rowr111/triangel/firmware/shared/ir_remote_mapping.jpg

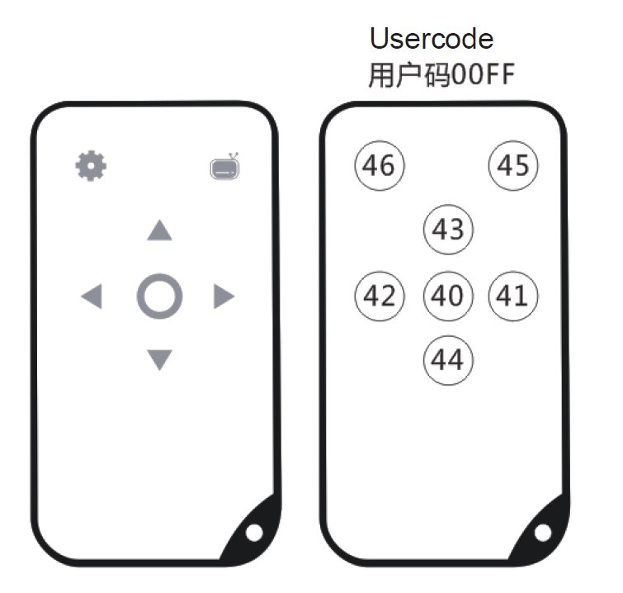
firmware/shared/ir_remote_mapping.jpg
