rowr111/triangel/graphics/triangel graphic.png

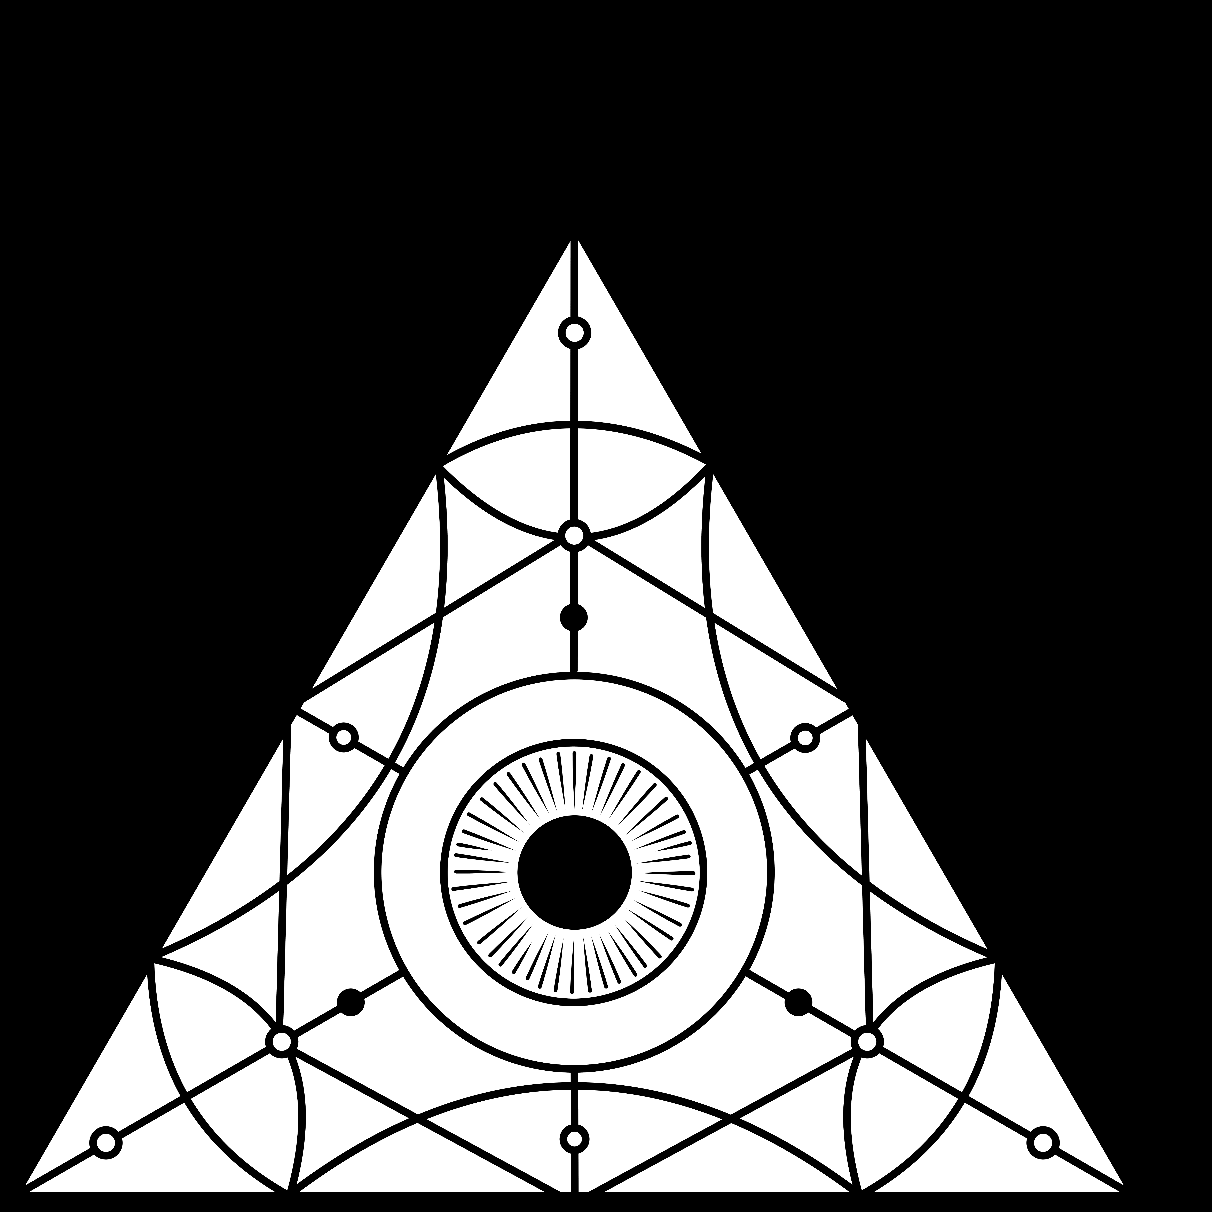
graphics/triangel graphic.png
