rowr111/triangel/graphics/triangel_input_overlay_L.jpg

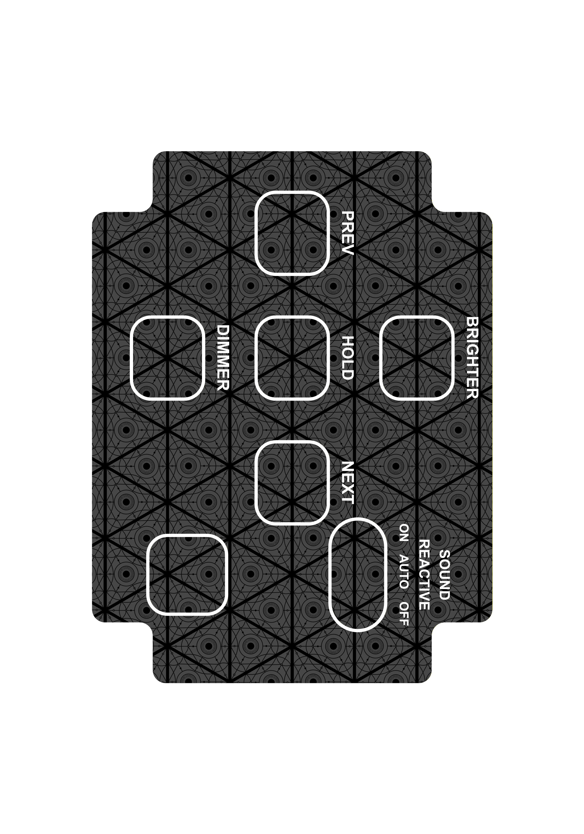
graphics/triangel_input_overlay_L.jpg
