rowr111/triangel/graphics/triangel_remote_overlay_L.jpg

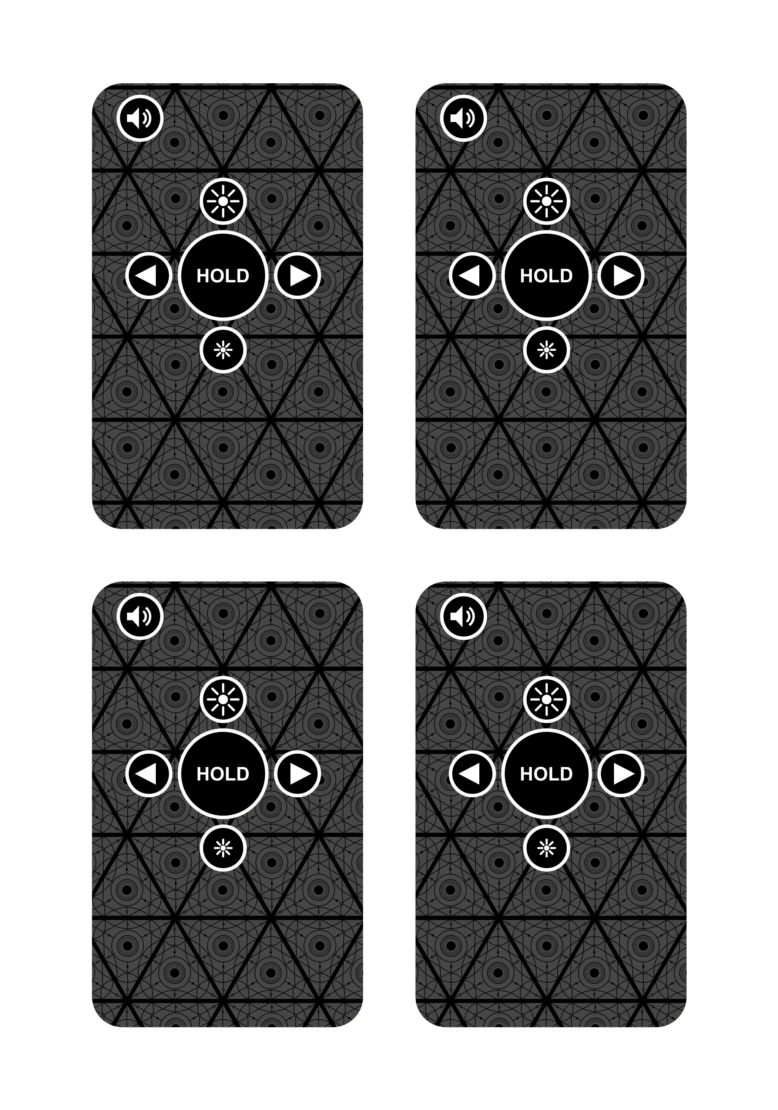
graphics/triangel_remote_overlay_L.jpg
