rowr111/triangel/graphics/triangle signature.png

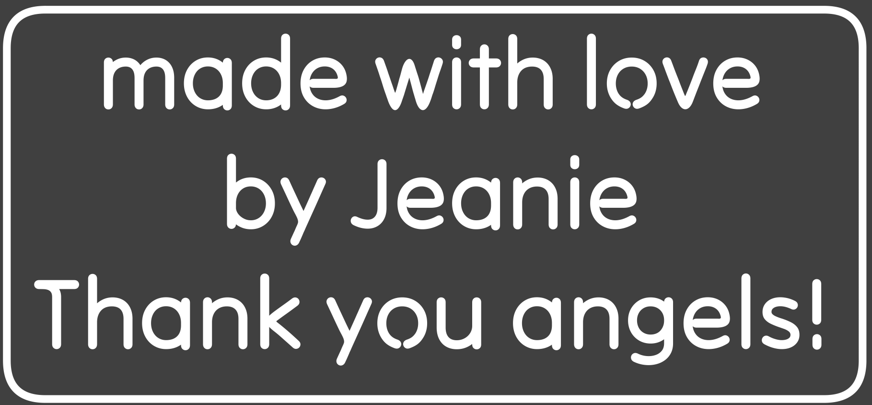
graphics/triangle signature.png
