rowr111/triangel/firmware/eye/src/patterns/ambient/flame.rs

use crate::led::geom::{BOARD_COUNT, BOARD_Y_RANGE, DIST_APEX};
use crate::patterns::{Frame, Pattern, cycle, knuth_hash, phase_phasors, ramp, PHASE_STEPS};
use crate::audio::Audio;
use crate::led::map::{LED_MAP, WORLD_BOT, WORLD_CX, WORLD_H, LED_COUNT};
use core::f32::consts::{PI, TAU};

const SECOND_WAVE_STRENGTH:    f32 = 0.5;  // second wave's amplitude, relative to the first
const SECOND_WAVELENGTH_RATIO: f32 = 1.7;  // second wave's wavelength, relative to the first
const SECOND_SPEED_RATIO:      f32 = 0.63; // second wave's speed, relative to the first
const WAVE_FLOOR:   f32 = 0.35; // brightness left in the wave troughs
const HEAT_BIAS:    f32 = 0.45; // heat added everywhere
const COOL_TILT:    f32 = 0.35;  // heat taken off at the top of the fixture
const TILE_TILT:    f32 = 0.25; // heat taken off at the top of each tile
const FLICKER_DEPTH: f32 = 0.35; // flicker swing around 1.0
const FLICKER_PERIOD_MS:  u32 = 628; // two unrelated periods, so the flicker
const FLICKER2_PERIOD_MS: u32 = 401; // looks like noise
const BREATHE_DEPTH: f32 = 0.15; // slow whole-flame swell
const BREATHE_PERIOD_MS: u32 = 3_700;
// Smoke: dark wisps that rise through the flame and wander sideways.
const SMOKE_DARKEN:  f32 = 0.7;   // how dark a wisp's core gets
const SMOKE_BAND_MM: f32 = 250.0; // vertical spacing between wisps
const SMOKE_MEANDER: f32 = 2.0;   // sideways wiggle depth, in radians
const SMOKE_MEANDER_MM: f32 = 300.0; // horizontal wavelength of the wiggle
const SMOKE_EDGE0: f32 = 0.72; // field value where a wisp starts
const SMOKE_EDGE1: f32 = 0.88; // field value where it is fully dark
const SMOKE_RISE_PERIOD_MS:    u32 = 5_100; // time to climb one band spacing
const SMOKE_MEANDER_PERIOD_MS: u32 = 8_900;
// Embers and tile flares
const EMBER_COUNT: usize = 5;        // embers in flight at once
const EMBER_PERIOD_MS:  u32 = 2_600; // base flight time
const EMBER_STAGGER_MS: u32 = 977;   // added per slot, so they respawn out of step
const EMBER_RISE_MM:   f32 = 260.0;  // how far an ember climbs
const EMBER_WOBBLE_MM: f32 = 25.0;   // sideways drift while rising
const EMBER_RADIUS_MM: f32 = 28.0;
const EMBER_HEAT:      f32 = 0.55;   // heat added at the ember's center
const FLARE_PERIOD_MS: u32 = 8_300;  // one random tile flares per period
const FLARE_LEN:  f32 = 0.25;        // flare length, as a fraction of the period
const FLARE_HEAT: f32 = 0.3;         // heat added across the flaring tile

// Q12 values are x4096, so 4096 is 1.0.
const ONE: i32 = 4096;
/// The two waves' weights in their mix, Q12.
const MIX1_Q: i32 = (4096.0 / (1.0 + SECOND_WAVE_STRENGTH)) as i32;
const MIX2_Q: i32 = (4096.0 * SECOND_WAVE_STRENGTH / (1.0 + SECOND_WAVE_STRENGTH)) as i32;
const WAVE_FLOOR_Q: i32 = (WAVE_FLOOR * 4096.0) as i32;
const HEAT_BIAS_Q: i32 = (HEAT_BIAS * 4096.0) as i32;
const FLICKER_HALF_Q: i32 = (FLICKER_DEPTH * 0.5 * 4096.0) as i32;
const SMOKE_DARKEN_Q: i32 = (SMOKE_DARKEN * 4096.0) as i32;
const SMOKE_EDGE0_Q: i32 = (SMOKE_EDGE0 * 4096.0) as i32;
/// Maps SMOKE_EDGE0..SMOKE_EDGE1 onto 0..1, Q12.
const SMOKE_EDGE_SCALE_Q: i32 = (4096.0 / (SMOKE_EDGE1 - SMOKE_EDGE0)) as i32;
/// SMOKE_MEANDER in turns x65536.
const SMOKE_MEANDER_TURNS: i32 = (SMOKE_MEANDER / TAU * 65536.0) as i32;
const FLARE_HEAT_Q: f32 = FLARE_HEAT * 4096.0;
const EMBER_HEAT_Q: f32 = EMBER_HEAT * 4096.0;
/// Ember radius in 1/16 mm, its square, and 1/radius^2 scaled to give Q12.
const EMBER_R_Q4: i32 = (EMBER_RADIUS_MM * 16.0) as i32;
const EMBER_R2_Q8: i32 = EMBER_R_Q4 * EMBER_R_Q4;
const EMBER_INV_R2: i32 = (4096 << 16) / EMBER_R2_Q8;

/// Sine table entries per turn; a phase in turns x65536 indexes it by its top bits.
const SIN_BITS: u32 = 10;
const SIN_STEPS: usize = 1 << SIN_BITS;
/// Fire ramp table entries across heat 0..1, plus one for exactly 1.0.
const RAMP_BITS: u32 = 10;
const RAMP_STEPS: usize = (1 << RAMP_BITS) + 1;

pub struct ApexFlame {
    pub speed:      f32, // mm/s outward, first wave
    pub wavelength: f32, // mm per cycle, first wave
    // sin and cos of each LED's phase in the two waves, Q12.
    w1_sin: [i16; LED_COUNT],
    w1_cos: [i16; LED_COUNT],
    w2_sin: [i16; LED_COUNT],
    w2_cos: [i16; LED_COUNT],
    // The same for its two flicker phases, Q12.
    f1_sin: [i16; LED_COUNT],
    f1_cos: [i16; LED_COUNT],
    f2_sin: [i16; LED_COUNT],
    f2_cos: [i16; LED_COUNT],
    // The smoke wiggle's phase by x, Q12, and the smoke field's phase by y, in turns x65536.
    m_sin:   [i16; LED_COUNT],
    m_cos:   [i16; LED_COUNT],
    smoke_y: [u16; LED_COUNT],
    // Heat taken off for the LED's height in the fixture and in its tile, Q12.
    cooling: [i16; LED_COUNT],
    // Position in 1/16 mm.
    x_q4: [i16; LED_COUNT],
    y_q4: [i16; LED_COUNT],
    sin_lut:  [i16; SIN_STEPS],
    ramp_lut: [[u8; 3]; RAMP_STEPS],
}

impl ApexFlame {
    pub fn new(speed: f32, wavelength: f32) -> Self {
        let k1 = TAU / wavelength;
        let k2 = TAU / (wavelength * SECOND_WAVELENGTH_RATIO);
        let q = |v: f32| (v * 4096.0).round() as i16;
        let (fl_sin, fl_cos) = phase_phasors();
        // Two hashed flicker phases per LED; phases stepping along the chain would look
        // like a sweep.
        let hash = |i: usize| knuth_hash(LED_MAP[i].chain_idx as u32);
        let k1_of = |i: usize| (hash(i) % PHASE_STEPS as u32) as usize;
        let k2_of = |i: usize| ((hash(i) >> 16) % PHASE_STEPS as u32) as usize;
        ApexFlame {
            speed,
            wavelength,
            w1_sin: core::array::from_fn(|i| q((DIST_APEX[i] * k1).sin())),
            w1_cos: core::array::from_fn(|i| q((DIST_APEX[i] * k1).cos())),
            w2_sin: core::array::from_fn(|i| q((DIST_APEX[i] * k2).sin())),
            w2_cos: core::array::from_fn(|i| q((DIST_APEX[i] * k2).cos())),
            f1_sin: core::array::from_fn(|i| q(fl_sin[k1_of(i)])),
            f1_cos: core::array::from_fn(|i| q(fl_cos[k1_of(i)])),
            f2_sin: core::array::from_fn(|i| q(fl_sin[k2_of(i)])),
            f2_cos: core::array::from_fn(|i| q(fl_cos[k2_of(i)])),
            m_sin: core::array::from_fn(|i| q((LED_MAP[i].wx / SMOKE_MEANDER_MM * TAU).sin())),
            m_cos: core::array::from_fn(|i| q((LED_MAP[i].wx / SMOKE_MEANDER_MM * TAU).cos())),
            smoke_y: core::array::from_fn(|i| {
                (LED_MAP[i].wy / SMOKE_BAND_MM * 65536.0) as u32 as u16
            }),
            cooling: core::array::from_fn(|i| {
                let led = &LED_MAP[i];
                let height = (WORLD_BOT - led.wy) / WORLD_H; // 0 at the apex, 1 at the top row
                let (y_min, y_max) = BOARD_Y_RANGE[led.board_id as usize];
                let local_height = (y_max - led.wy) / (y_max - y_min).max(1.0);
                q(height * COOL_TILT + local_height * TILE_TILT)
            }),
            x_q4: core::array::from_fn(|i| (LED_MAP[i].wx * 16.0).round() as i16),
            y_q4: core::array::from_fn(|i| (LED_MAP[i].wy * 16.0).round() as i16),
            sin_lut: core::array::from_fn(|k| q((k as f32 / SIN_STEPS as f32 * TAU).sin())),
            ramp_lut: core::array::from_fn(|k| fire_ramp(k as f32 / (1 << RAMP_BITS) as f32)),
        }
    }
}

/// A float in -1..1 as Q12.
fn q12(v: f32) -> i32 {
    (v * 4096.0).round() as i32
}

/// sin(a + b) in Q12, from the sin and cos of each.
fn sin_sum_q12(a_sin: i16, a_cos: i16, b_sin: i32, b_cos: i32) -> i32 {
    (a_sin as i32 * b_cos + a_cos as i32 * b_sin) >> 12
}

impl Pattern for ApexFlame {
    fn render(&mut self, t_ms: u32, _audio: &Audio, out: &mut Frame) {
        // Each time term wraps at its own period first, so the f32 stays precise.
        let wl2  = self.wavelength * SECOND_WAVELENGTH_RATIO;
        let spd2 = self.speed * SECOND_SPEED_RATIO;
        let p1_ms = (self.wavelength / self.speed * 1000.0) as u32;
        let p2_ms = (wl2 / spd2 * 1000.0) as u32;
        let t1_s = (t_ms % p1_ms.max(1)) as f32 / 1000.0;
        let t2_s = (t_ms % p2_ms.max(1)) as f32 / 1000.0;
        let flick_phase   = cycle(t_ms, FLICKER_PERIOD_MS) * TAU;
        let flick2_phase  = cycle(t_ms, FLICKER2_PERIOD_MS) * TAU;
        let breathe_phase = cycle(t_ms, BREATHE_PERIOD_MS) * TAU;
        let breathe = q12(1.0 - BREATHE_DEPTH * (0.5 + 0.5 * breathe_phase.sin()));
        let smoke_rise = ((t_ms % SMOKE_RISE_PERIOD_MS) * 65536 / SMOKE_RISE_PERIOD_MS) as u16; // turns x65536
        let smoke_meander = cycle(t_ms, SMOKE_MEANDER_PERIOD_MS) * TAU;

        // sin and cos of this frame's angle for the waves, the flicker and the smoke wiggle.
        let (b1_sin, b1_cos) = (-t1_s * self.speed * (TAU / self.wavelength)).sin_cos();
        let (b2_sin, b2_cos) = (-t2_s * spd2 * (TAU / wl2)).sin_cos();
        let (f1_sin, f1_cos) = flick_phase.sin_cos();
        let (f2_sin, f2_cos) = flick2_phase.sin_cos();
        let (m_sin, m_cos) = smoke_meander.sin_cos();
        let (b1_sin, b1_cos, b2_sin, b2_cos) = (q12(b1_sin), q12(b1_cos), q12(b2_sin), q12(b2_cos));
        let (f1_sin, f1_cos, f2_sin, f2_cos) = (q12(f1_sin), q12(f1_cos), q12(f2_sin), q12(f2_cos));
        let (m_sin, m_cos) = (q12(m_sin), q12(m_cos));

        // Embers start low inside the triangle, rise with a wobble and fade.
        let mut embers = [(0i32, 0i32, 0i32); EMBER_COUNT]; // (x, y in 1/16 mm, heat Q12)
        for (k, ember) in embers.iter_mut().enumerate() {
            let period = EMBER_PERIOD_MS + k as u32 * EMBER_STAGGER_MS;
            let phase = cycle(t_ms, period);
            let h = knuth_hash(t_ms / period) ^ (k as u32).wrapping_mul(0x9E37_79B9);
            let y0 = WORLD_BOT - 6.0 - ((h >> 8) % 130) as f32;
            let half_w = (WORLD_BOT - y0) / WORLD_H * 250.0; // triangle half-width at y0
            let x0 = WORLD_CX + ((h % 201) as f32 - 100.0) / 100.0 * half_w;
            let x = x0 + (phase * TAU * 1.5 + (h >> 16) as f32).sin() * EMBER_WOBBLE_MM;
            let y = y0 - phase * EMBER_RISE_MM;
            *ember = (
                (x * 16.0).round() as i32,
                (y * 16.0).round() as i32,
                (EMBER_HEAT_Q * (phase * PI).sin()) as i32,
            );
        }

        // One random tile per period flares up fast and settles slowly.
        let flare_phase = cycle(t_ms, FLARE_PERIOD_MS);
        let flare_board = 1 + (knuth_hash(t_ms / FLARE_PERIOD_MS) >> 8) % BOARD_COUNT as u32;
        let flare_env = if flare_phase < FLARE_LEN {
            let fp = flare_phase / FLARE_LEN;
            (fp * 6.0).min(1.0) * (1.0 - fp)
        } else {
            0.0
        };
        let flare_heat = (FLARE_HEAT_Q * flare_env) as i32;

        for (i, led) in LED_MAP.iter().enumerate() {
            let w1 = sin_sum_q12(self.w1_sin[i], self.w1_cos[i], b1_sin, b1_cos);
            let w2 = sin_sum_q12(self.w2_sin[i], self.w2_cos[i], b2_sin, b2_cos);
            let wave = (((w1 * MIX1_Q + w2 * MIX2_Q) >> 12) + ONE) >> 1;
            let wave = WAVE_FLOOR_Q + (((ONE - WAVE_FLOOR_Q) * wave) >> 12);

            // Smoke: rising bands that wiggle sideways, dark where the field is near its peak.
            let wiggle = sin_sum_q12(self.m_sin[i], self.m_cos[i], m_sin, m_cos);
            let turn = self.smoke_y[i]
                .wrapping_add(smoke_rise)
                .wrapping_add(((wiggle * SMOKE_MEANDER_TURNS) >> 12) as u16);
            // Sine table lookup, interpolated between entries.
            let step = (turn >> (16 - SIN_BITS)) as usize;
            let s0 = self.sin_lut[step] as i32;
            let s1 = self.sin_lut[(step + 1) & (SIN_STEPS - 1)] as i32;
            let part = (turn & ((1 << (16 - SIN_BITS)) - 1)) as i32;
            let sine = s0 + (((s1 - s0) * part) >> (16 - SIN_BITS));
            let field = (sine + ONE) >> 1;
            let wisp = (((field - SMOKE_EDGE0_Q) * SMOKE_EDGE_SCALE_Q) >> 12).clamp(0, ONE);
            let wisp = (((wisp * wisp) >> 12) * (3 * ONE - 2 * wisp)) >> 12; // smoothstep
            let smoke = ONE - ((SMOKE_DARKEN_Q * wisp) >> 12);

            let fl1 = sin_sum_q12(self.f1_sin[i], self.f1_cos[i], f1_sin, f1_cos);
            let fl2 = sin_sum_q12(self.f2_sin[i], self.f2_cos[i], f2_sin, f2_cos);
            let flicker = ONE + ((FLICKER_HALF_Q * (fl1 + fl2)) >> 12);

            // Nearby embers and the flaring tile.
            let mut event_heat = 0i32;
            for &(ex, ey, heat) in &embers {
                let dx = self.x_q4[i] as i32 - ex;
                let dy = self.y_q4[i] as i32 - ey;
                if dx.abs() >= EMBER_R_Q4 || dy.abs() >= EMBER_R_Q4 {
                    continue;
                }
                let d2 = dx * dx + dy * dy;
                if d2 < EMBER_R2_Q8 {
                    let fall = ((EMBER_R2_Q8 - d2) * EMBER_INV_R2) >> 16;
                    event_heat += (heat * fall) >> 12;
                }
            }
            if led.board_id as u32 == flare_board {
                event_heat += flare_heat;
            }

            let lit = (((wave * flicker) >> 12) * breathe) >> 12;
            let heat = ((lit + HEAT_BIAS_Q - self.cooling[i] as i32 + event_heat) * smoke) >> 12;
            out[i] = self.ramp_lut[(heat.clamp(0, ONE) >> (12 - RAMP_BITS)) as usize];
        }
    }
}

/// Color for a heat in 0..1. The coolest stop is a dim ember, not black.
fn fire_ramp(heat: f32) -> [u8; 3] {
    const STOPS: [(f32, [f32; 3]); 6] = [
        (0.00, [25.0, 3.0, 0.0]),      // dim ember
        (0.30, [180.0, 10.0, 0.0]),    // deep red
        (0.55, [255.0, 110.0, 0.0]),   // orange
        (0.75, [255.0, 230.0, 40.0]),  // bright yellow
        (0.90, [255.0, 255.0, 200.0]), // white
        (1.00, [170.0, 210.0, 255.0]), // blue-white
    ];
    let c = ramp(&STOPS, heat);
    [c[0] as u8, c[1] as u8, c[2] as u8]
}
