rowr111/triangel/firmware/eye/src/diag.rs

use std::sync::Mutex;

// USB-serial diagnostic channel for bringup on hardware. The console input
// path is unavailable on this system build (UART2 is repurposed for the ear
// audio link), so these unconditionally streamed lines are the only
// visibility into the firmware. Active only on builds with `usb` and without
// `previewer` - the previewer's serial stream carries binary LED frames and
// text mixed in would corrupt it. On all other builds every call compiles to
// a no-op.

/// Boot milestones, printed as reached and repeated in the heartbeat line so
/// a monitor attached late can still see how far boot got.
#[derive(Clone, Copy)]
pub enum Stage {
    MainStart,
    LedOutUp,
    AudioUp,
    InputSpawned,
    RenderLoop,
}

impl Stage {
    fn name(self) -> &'static str {
        match self {
            Stage::MainStart => "main start",
            Stage::LedOutUp => "led out up",
            Stage::AudioUp => "audio up",
            Stage::InputSpawned => "input spawned",
            Stage::RenderLoop => "render loop",
        }
    }
}

static STAGE: Mutex<Stage> = Mutex::new(Stage::MainStart);

pub struct Diag {
    #[cfg(all(feature = "usb", not(feature = "previewer")))]
    usb: usb_bao1x::UsbHid,
}

impl Diag {
    pub fn new() -> Self {
        Self {
            #[cfg(all(feature = "usb", not(feature = "previewer")))]
            usb: usb_bao1x::UsbHid::new(),
        }
    }

    /// Send one diagnostic line to the USB serial port (no-op on builds
    /// without it). One send per line: text and line ending in separate sends
    /// let lines from different threads interleave mid-line.
    pub fn line(&self, s: &str) {
        #[cfg(all(feature = "usb", not(feature = "previewer")))]
        {
            let mut out = String::with_capacity(s.len() + 2);
            out.push_str(s);
            out.push_str("\r\n");
            self.usb.serial_send(out.as_bytes()).ok();
        }
        #[cfg(not(all(feature = "usb", not(feature = "previewer"))))]
        let _ = s;
    }
}

/// Record a boot stage and print it.
pub fn stage(diag: &Diag, stage: Stage) {
    *STAGE.lock().unwrap() = stage;
    diag.line(&format!("eye boot: {}", stage.name()));
}

/// Report liveness and IR activity: one line shortly after boot, then a line
/// at most every 5 seconds and only when the IR counters have changed - the
/// steady-state serial output is silent. Spawned before anything that could
/// block in main so a stalled boot still heartbeats and names the stage it
/// is stuck at.
pub fn spawn_heartbeat() {
    #[cfg(all(feature = "usb", not(feature = "previewer")))]
    std::thread::spawn(|| {
        let tt = ticktimer::Ticktimer::new().unwrap();
        let diag = Diag::new();
        diag.line("heartbeat thread up");
        let mut last_stats = None;
        let mut last_audio = None;
        loop {
            tt.sleep_ms(5000).ok();

            // Audio link: counters first, so bytes-but-no-frames is distinguishable
            // from nothing arriving at all.
            let link = crate::audio::stats();
            if last_audio != Some((link.frames_ok, link.frames_bad)) {
                last_audio = Some((link.frames_ok, link.frames_bad));
                diag.line(&format!(
                    "audio: status {}, frames {}, dropped {}, first byte {:02x}, {:.1} dBFS, norm {:.2}",
                    link.status, link.frames_ok, link.frames_bad, link.first_byte, link.dbfs, link.norm,
                ));
                let bass = crate::audio::drop_stats();
                diag.line(&format!(
                    "drop: {}, drops {}, bass {:.1} dB against {:.1} dB",
                    if bass.in_breakdown { "in breakdown" } else { "normal" },
                    bass.drops, bass.bass_db, bass.ref_db,
                ));
            }

            let ir = crate::input::ir::stats();
            if last_stats == Some(ir) {
                continue;
            }
            last_stats = Some(ir);
            let stage = *STAGE.lock().unwrap();
            diag.line(&format!(
                "alive {} s, stage: {}, ir: decoded {}, rejected {}, clock {} Hz, last frame {:08x}",
                tt.elapsed_ms() / 1000,
                stage.name(),
                ir.decoded,
                ir.rejected,
                ir.clock_hz,
                ir.last_frame,
            ));
        }
    });
}
